SeanAvery/lte-rover/camera/vision-os/camera/include/sensor_i2c.h

static struct msm_camera_i2c_reg_array init_array_imx298[] = {
  {0x101,0x0,0},  // IMAGE_ORIENT
  {0x601,0x0,0},  // test pattern
  //{0xb02,0,0},    // green correction?
  // external clock setting
  {0x136,0x18,0}, {0x137,0x0,0}, // EXCK_FREQ = Extclk_frequency_mhz
  // global setting?
  {0x30f4,0x1,0},
  {0x30f5,0x7a,0},
  {0x30f6,0x0,0},
  {0x30f7,0xec,0},
  {0x30fc,0x1,0},
  {0x3101,0x1,0},
  {0x5b2f,0x8,0},
  {0x5d32,0x5,0},
  {0x5d7c,0x0,0},
  {0x5d7d,0x0,0},
  {0x5db9,0x1,0},
  {0x5e43,0x0,0},
  {0x6300,0x0,0},
  {0x6301,0xea,0},
  {0x6302,0x0,0},
  {0x6303,0xb4,0},
  {0x6564,0x0,0},
  {0x6565,0xb6,0},
  {0x6566,0x0,0},
  {0x6567,0xe6,0},
  {0x6714,0x1,0},
  {0x6758,0xb,0},
  {0x6910,0x4,0},
  {0x6916,0x1,0},
  {0x6918,0x4,0},
  {0x691e,0x1,0},
  {0x6931,0x1,0},
  {0x6937,0x2,0},
  {0x693b,0x2,0},
  {0x6d00,0x4a,0},
  {0x6d01,0x41,0},
  {0x6d02,0x23,0},
  {0x6d05,0x4c,0},
  {0x6d06,0x10,0},
  {0x6d08,0x30,0},
  {0x6d09,0x38,0},
  {0x6d0a,0x2c,0},
  {0x6d0b,0x2d,0},
  {0x6d0c,0x34,0},
  {0x6d0d,0x42,0},
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
  // PDAF stuff
  {0x3166,0x1,0}, //AREA_EN_0
  {0x3167,0x1,0},
  {0x3168,0x1,0},
  {0x3169,0x1,0},
  {0x316a,0x1,0},
  {0x316b,0x1,0},
  {0x316c,0x1,0},
  {0x316d,0x1,0},
  {0x3158,0x2,0},
  {0x3159,0x2,0},
  {0x315a,0x2,0},
  {0x315b,0x3,0},
  {0x3013,0x7,0}, //RMSC_NR_MODE
  {0x3035,0x1,0},
  {0x3051,0x0,0},
  {0x3056,0x2,0},
  {0x3057,0x1,0},
  {0x3060,0x0,0},
  {0x8435,0x0,0},
  {0x8455,0x0,0},
  {0x847c,0x0,0},
  {0x84fb,0x1,0},
  {0x9619,0xa0,0},
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
};
