SeanAvery/lte-rover/camera/controllerd/main.cpp

#include <iostream>
#include <sys/socket.h>
#include <arpa/inet.h>
#include <unistd.h>

#include "messaging/messaging.h"
#include "gen/cpp/car.capnp.h"


#define UDP_PORT 900
#define UDP_HOST "192.168.1.5"
#define BUF_MAX 1024

#define CONTROLLERD_FREQUENCY 10000 // 100 hz

int main()
{
  std::cout << "starting controller daemon" << std::endl;

  // init udp socket
  int sockfd;
  sockfd = socket(AF_INET, SOCK_DGRAM, 0);
  struct sockaddr_in serv, client;
  serv.sin_family = AF_INET;
  serv.sin_addr.s_addr = inet_addr(UDP_HOST);
  serv.sin_port = htons(UDP_PORT);

  int err = bind(sockfd, (const struct sockaddr *)&serv, sizeof(serv));
  if (err != 0)
  {
    std::cout << "error binding socket: " << err << std::endl;
  }

  // init publisher
  std::string endpoint = "controls";
  Context * context = Context::create();
  PubSocket *publisher = PubSocket::create(context, endpoint);

  // init data container
  char buffer[BUF_MAX];
  socklen_t len = sizeof(client);

  while (1)
  {
    usleep(CONTROLLERD_FREQUENCY);
    // check socket for msg
    std::cout << "checking socket" << std::endl;
    ssize_t n = recvfrom(sockfd, (char *)buffer, BUF_MAX, MSG_WAITALL, (struct sockaddr *) &client, &len);

    std::cout << "udp msg: " << buffer << std::endl;

    // publish message
    publisher->send(buffer, sizeof(buffer));
  }
}
