SeanAvery/lte-rover/camera/camerad/main.cpp

#include <iostream>
#include "Camera.cpp"

int main() {
  std::cout << "Camera process starting" << std::endl;

  Camera cam;
  cam.camera_init();
  cam.camera_open();
  cam.camera_run();
  return 0;
}
