SeanAvery/lte-rover/camera/camerad/Camera.h

#include <string>
#include <fstream>
#include <thread>

#include <linux/ioctl.h>
#include <linux/videodev2.h>

#include "utils.h"

#include "include/msm_camsensor_sdk.h"
#include "sensor_i2c.h"
#include "include/msm_cam_sensor.h"
#include "include/msmb_camera.h"
#include "include/msmb_isp.h"
#include "include/msmb_ispif.h"

#include "messaging/messaging.h"
#include "visionipc/visionbuf.h"
#include "visionipc/visionipc.h"

#define FRAME_BUF_COUNT 4
#define METADATA_BUF_COUNT 4

namespace params
{
  char CSID_SUBSYSTEM[] = "/dev/v4l-subdev3";
  char CSIPHY_SUBSYSTEM[] = "/dev/v4l-subdev0";
  char ISP_SUBSYSTEM[] = "/dev/v4l-subdev13";
  char ACTUATOR_SUBSYSTEM[] = "/dev/v4l-subdev7";
  char SENSOR_SUBSYSTEM[] = "/dev/v4l-subdev17";
  // char SENSOR_SUBSYSTEM[] = "/dev/v4l-subdev18";
  char SENSORINIT_SUBSYSTEM[] = "/dev/v4l-subdev11";
  char MSM_SUBSYSTEM[] = "/dev/media0";
  char V4L_SUBSYSTEM[] = "/dev/video0";
  char ISPIF_SUBSYSTEM[] = "/dev/v4l-subdev15";
}

typedef struct StreamState {
  struct msm_isp_buf_request buf_request;
  struct msm_vfe_axi_stream_request_cmd stream_req;
  struct msm_isp_qbuf_info qbuf_info[FRAME_BUF_COUNT];
  // VisionBuf *bufs;
} StreamState;

class Camera
{
  private:
    int csid_fd;
    int csiphy_fd;
    int isp_fd;
    int sensor_fd;
    int actuator_fd;
    unique_fd sensorinit_fd;

    int msm_fd;
    int v4l_fd;
    int ispif_fd;

    uint32_t pixel_clock;

    struct msm_vfe_axi_stream_cfg_cmd stream_cfg;

    StreamState ss[3];

    int BringUp();
    int Shutdown();

  public:
    void camera_init();
    void camera_open();
    void camera_run();
    void camera_start();
    void camera_process(); // thread event
    int sensor_write_regs(struct msm_camera_i2c_reg_array* arr, size_t size, msm_camera_i2c_data_type data_type);
};
